RobertLukan/rpi-cm4-custom-board/pictures/PXL_20240108_123218701.jpg

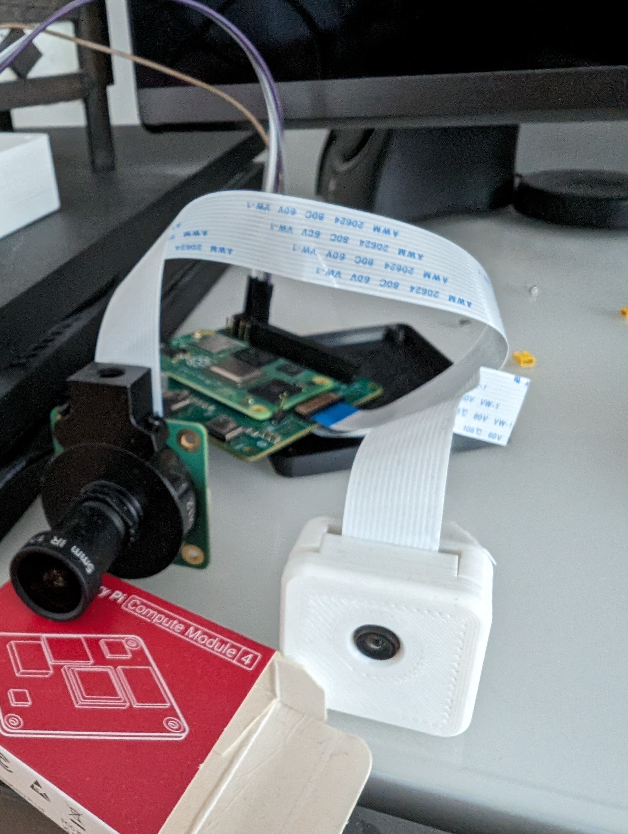
pictures/PXL_20240108_123218701.jpg
